b-wave/PROJECT-27/BMP/103_GTRANS.bmp

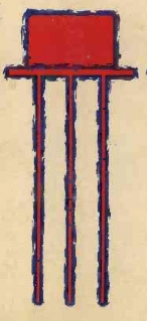
BMP/103_GTRANS.bmp
