b-wave/PROJECT-27/BMP/MK1_SCHpng.png

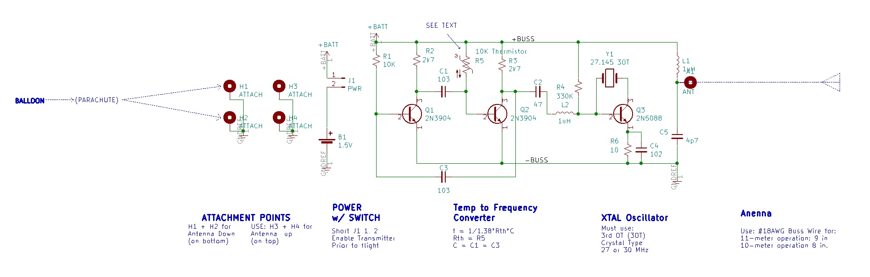
BMP/MK1_SCHpng.png
