b-wave/PROJECT-27/BMP/proj27_sch_v3.png

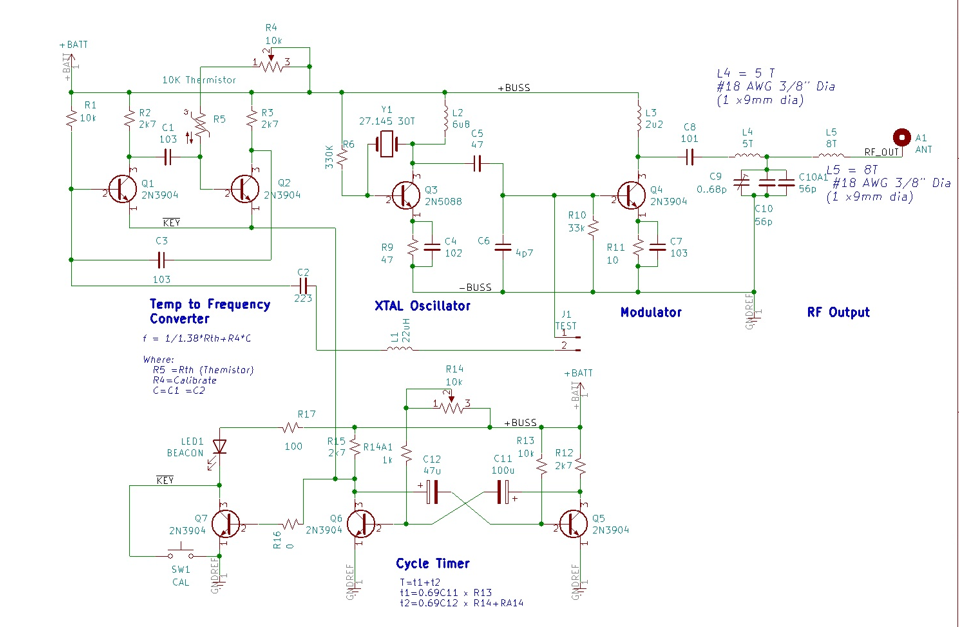
BMP/proj27_sch_v3.png
