b-wave/PROJECT-27/BMP/proj27-parts.png

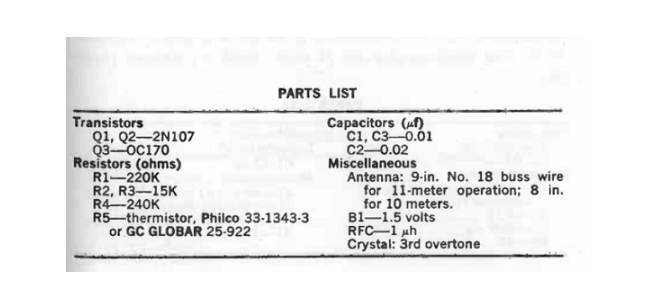
BMP/proj27-parts.png
